IoTopenTech/Nodo_TTN_MAD_V2/software/WIFI_HALL_BME280_FRAM/esp03/README.MD

Este ejemplo permite al ESP-03 levantar un portal cautivo mediante el que el usuario puede configurar la activación (OTAA o ABP) del nodo.
