IoTopenTech/Nodo_TTN_MAD_V2/rsc/TTN_MAD_V2_2.jpg

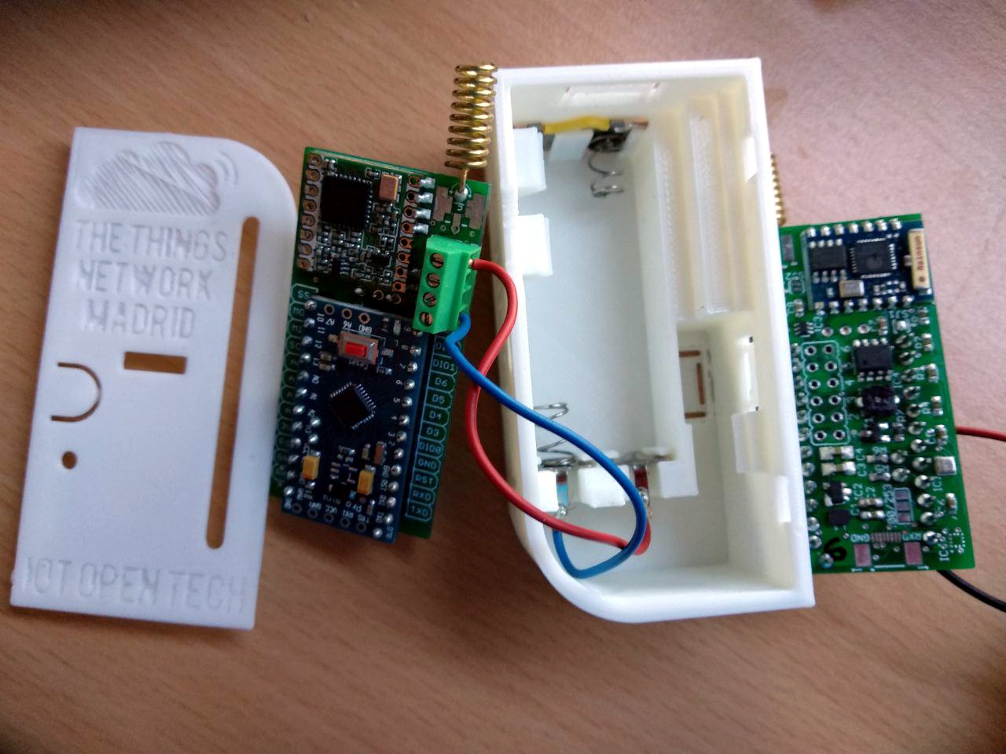
rsc/TTN_MAD_V2_2.jpg
