IoTopenTech/Nodo_TTN_MAD_V2/rsc/TTN_MAD_V2_2_lowpower.jpg

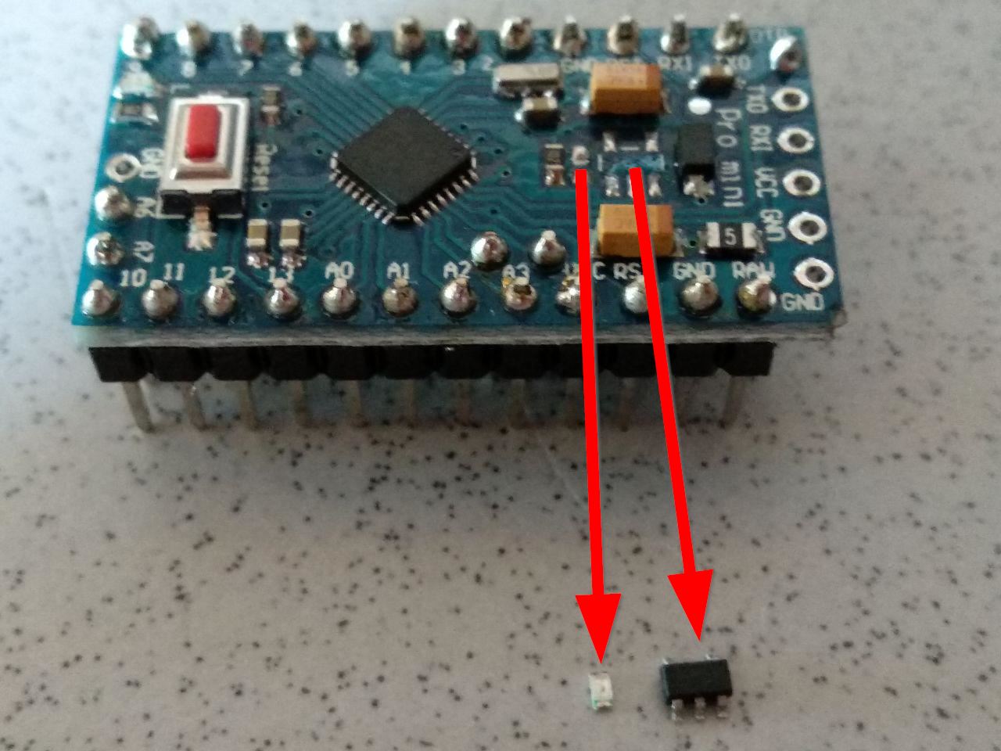
rsc/TTN_MAD_V2_2_lowpower.jpg
