IoTopenTech/Nodo_TTN_MAD_V2/rsc/ttn_mad_v2_completo.jpg

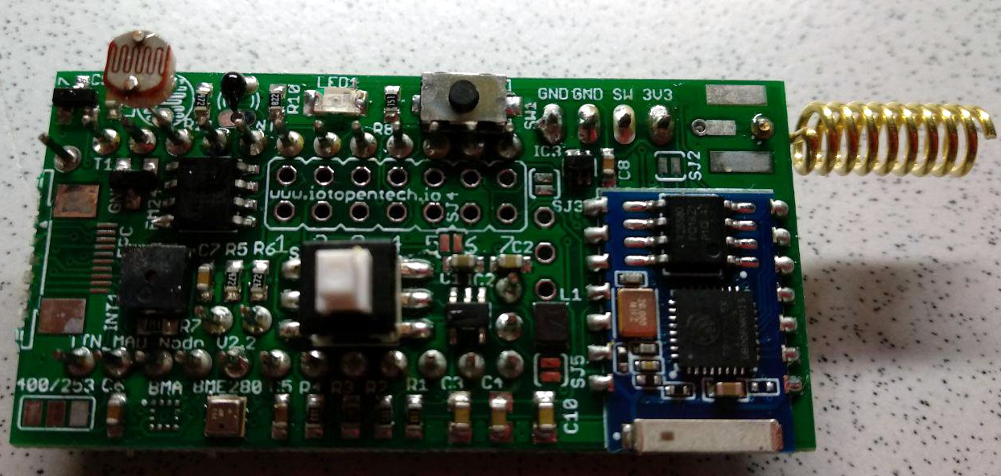
rsc/ttn_mad_v2_completo.jpg
