IoTopenTech/Nodo_TTN_MAD_V2/rsc/ttn_mad_v2_pcb.jpg

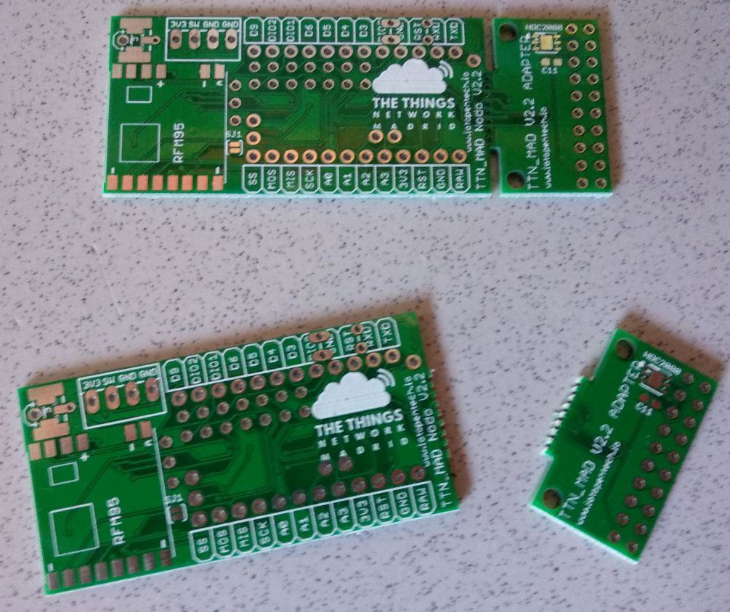
rsc/ttn_mad_v2_pcb.jpg
